Sithum02/SLAP-Sonic-ParkAssist/Enclosure/Enclosure Screenshots/Screenshot 2024-08-24 115755.png

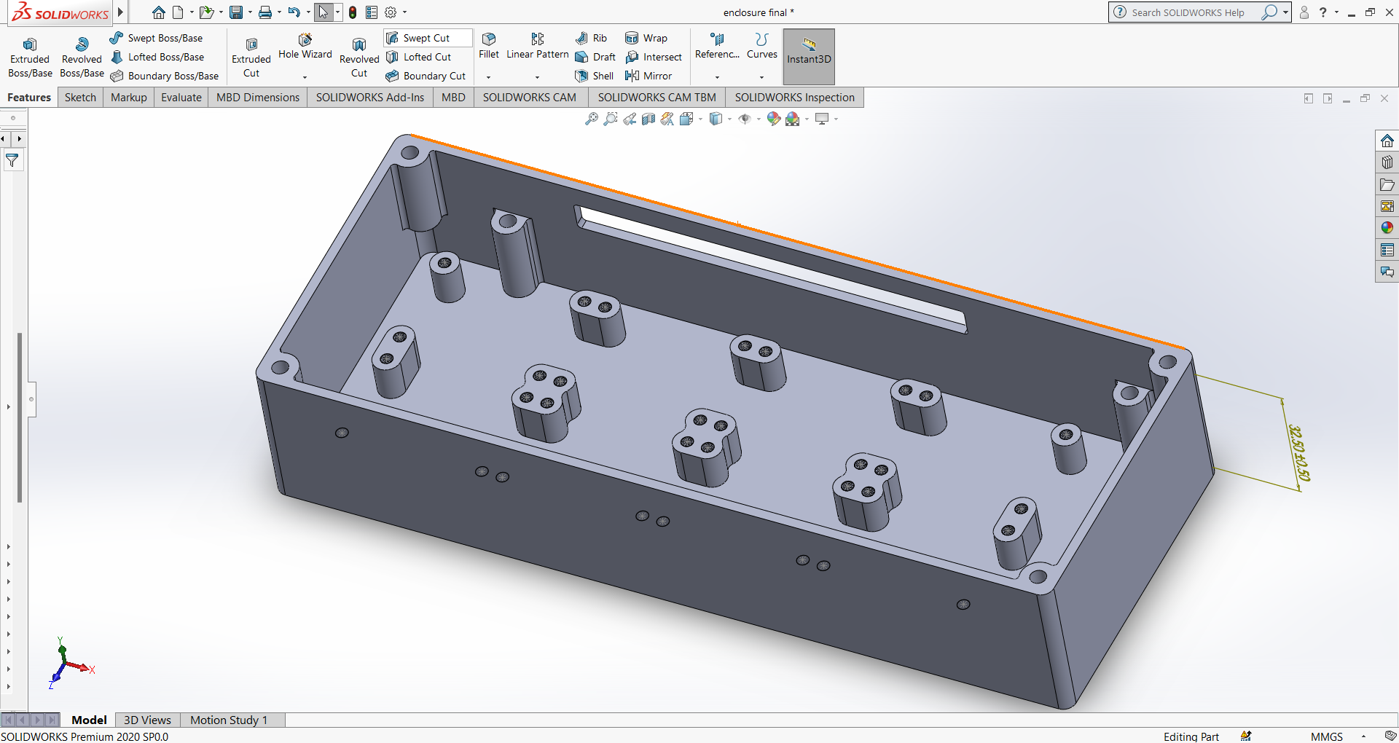
Enclosure/Enclosure Screenshots/Screenshot 2024-08-24 115755.png
