Sithum02/SLAP-Sonic-ParkAssist/PCB/PCB-Bottom.png

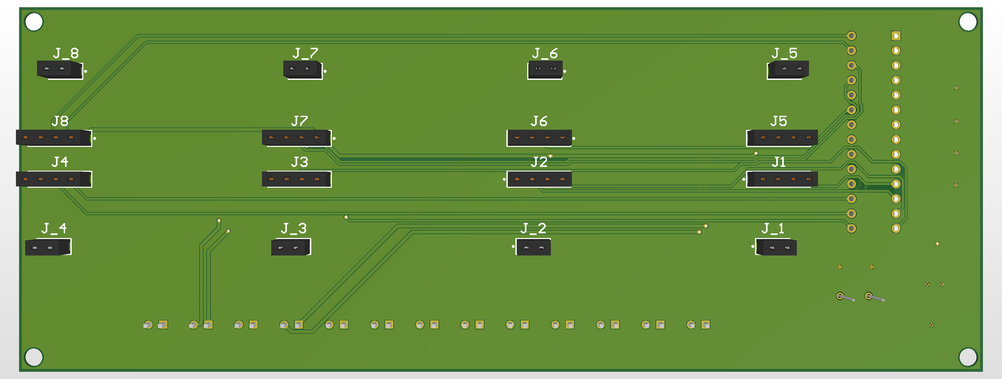
PCB/PCB-Bottom.png
