Sithum02/SLAP-Sonic-ParkAssist/User Manual/SLAP Sonic ParkAssist User Manual.png

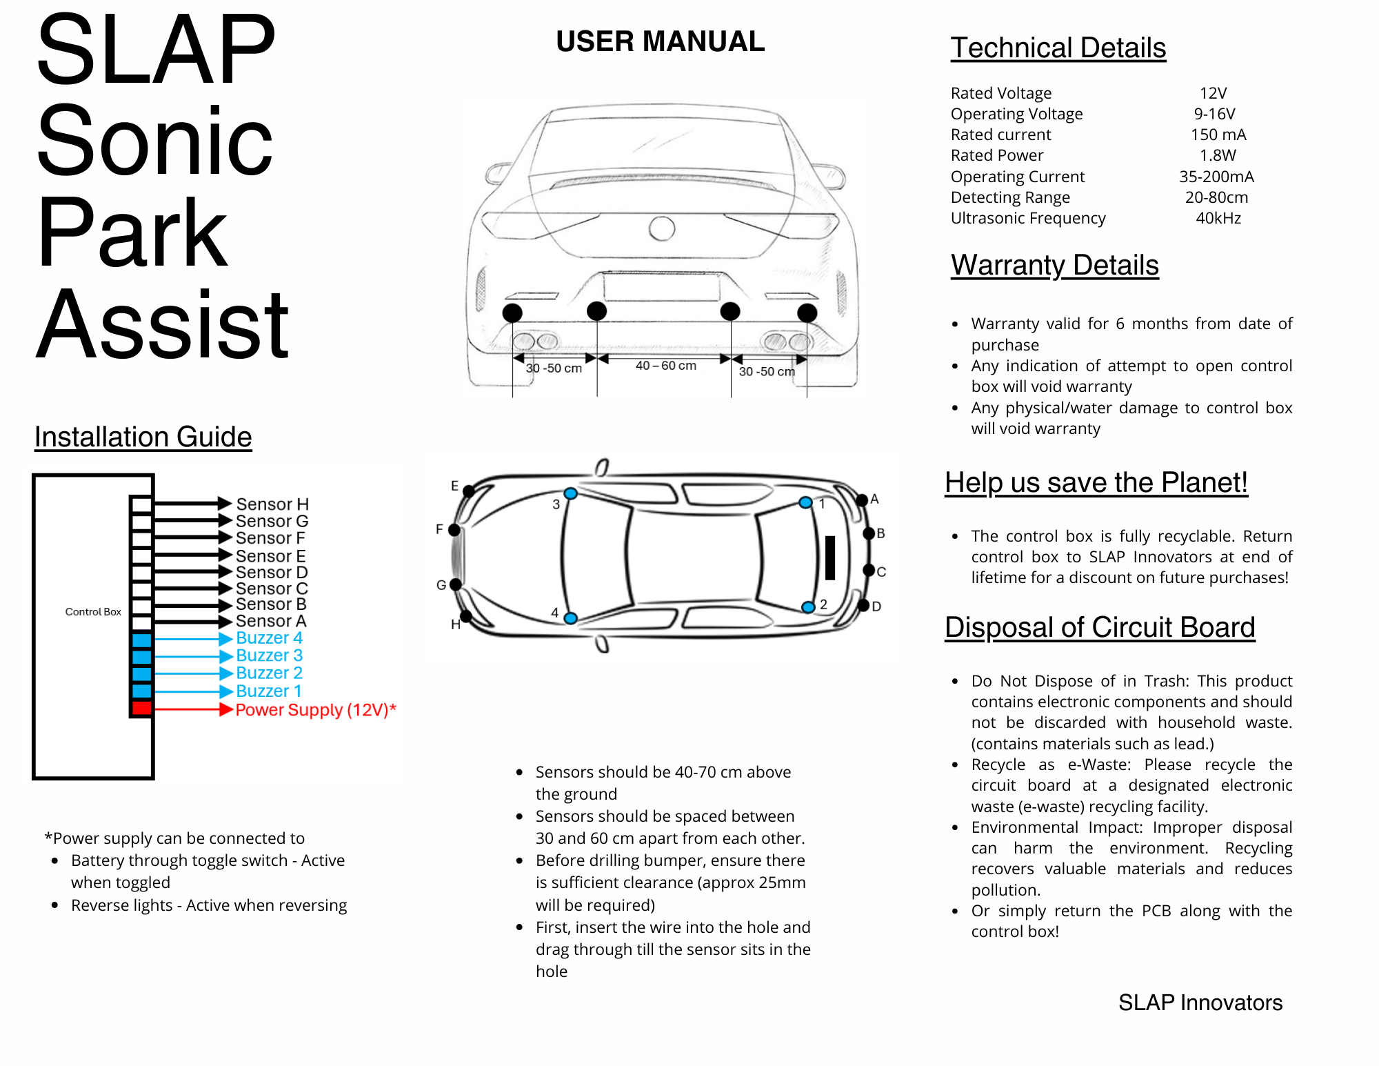
User Manual/SLAP Sonic ParkAssist User Manual.png
